nckhrdy/EchoView.ai/Device/TeensyDevDemos/Arduino/OLED_1in5_b/OLED_1in5_b.cpp

/*****************************************************************************
* | File        :   OLED_1in5_b.c
* | Author      :   Waveshare team
* | Function    :   1.5inch OLED Module (B) Drive function
* | Info        :
*----------------
* | This version:   V1.0
* | Date        :   2023-05-20
* | Info        :
* -----------------------------------------------------------------------------
#
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
******************************************************************************/
#include "OLED_1in5_b.h"
#include "stdio.h"
#include "DEV_Config.h"
/*******************************************************************************
function:
            Hardware reset
*******************************************************************************/
static void OLED_Reset(void)
{
    OLED_RST_1;
    Driver_Delay_ms(100);
    OLED_RST_0;
    Driver_Delay_ms(100);
    OLED_RST_1;
    Driver_Delay_ms(100);
}

/*******************************************************************************
function:
            Write register address and data
*******************************************************************************/
static void OLED_WriteReg(uint8_t Reg)
{
#if USE_SPI
    OLED_DC_0;
    DEV_SPI_WriteByte(Reg);
#elif USE_IIC
    I2C_Write_Byte(Reg, IIC_CMD);
#endif
}

static void OLED_WriteData(uint8_t Data)
{
#if USE_SPI
    OLED_DC_1;
    DEV_SPI_WriteByte(Data);
#elif USE_IIC
    I2C_Write_Byte(Data, IIC_RAM);
#endif
}

/*******************************************************************************
function:
            Common register initialization
*******************************************************************************/
static void OLED_InitReg(void)
{
    OLED_WriteReg(0xae); /*turn off OLED display*/
    OLED_WriteReg(0x00); /*set lower column address*/
    OLED_WriteReg(0x10); /*set higher column address*/

    OLED_WriteReg(0xB0); /*set page address*/

    OLED_WriteReg(0xdc); /*set display start line*/
    OLED_WriteReg(0x20);

    OLED_WriteReg(0x81); /*contract control*/
    OLED_WriteReg(0x6f); /*128*/

    OLED_WriteReg(0x21); /* Set Memory addressing mode (0x20/0x21) */

    OLED_WriteReg(0xa1); /*set segment remap*/

    OLED_WriteReg(0xc0); /*Com scan direction*/

    OLED_WriteReg(0xa4); /*Disable Entire Display On (0xA4/0xA5)*/

    OLED_WriteReg(0xa6); /*normal / reverse*/

    OLED_WriteReg(0xa8); /*multiplex ratio*/
    OLED_WriteReg(0x7f); /*duty = 1/64*/

    OLED_WriteReg(0xd3); /*set display offset*/
    OLED_WriteReg(0x60);

    OLED_WriteReg(0xd5); /*set osc division*/
    OLED_WriteReg(0x80);

    OLED_WriteReg(0xd9); /*set pre-charge period*/
    OLED_WriteReg(0x1d);

    OLED_WriteReg(0xdb); /*set vcomh*/
    OLED_WriteReg(0x35);

    OLED_WriteReg(0xad); /*set charge pump enable*/
    OLED_WriteReg(0x80); /*Set DC-DC enable (a=0:disable; a=1:enable) */
}

/********************************************************************************
function:
            initialization
********************************************************************************/
void OLED_1in5_B_Init()
{
    System_Init();
    // Hardware reset
    OLED_Reset();
    // Set the initialization register

    OLED_InitReg();
    Driver_Delay_ms(200);

    // Turn on the OLED display
    OLED_WriteReg(0xaf);
}

/********************************************************************************
function:
            Clear screen
********************************************************************************/
void OLED_1in5_B_Clear()
{
    UWORD Width, Height, column;
    Width = (OLED_1in5_B_WIDTH % 8 == 0) ? (OLED_1in5_B_WIDTH / 8) : (OLED_1in5_B_WIDTH / 8 + 1);
    Height = OLED_1in5_B_HEIGHT;

    OLED_WriteReg(0xb0); // Set the row  start address
    for (UWORD j = 0; j < Height; j++)
    {
        column = j;
        OLED_WriteReg(0x00 + (column & 0x0f)); // Set column low start address
        OLED_WriteReg(0x10 + (column >> 4));   // Set column higt start address
        for (UWORD i = 0; i < Width; i++)
        {
            OLED_WriteData(0x00);
        }
    }
}
void OLED_1in5_B_Clear_Black(void)
{
    UWORD Width, Height, column;
    Width = (OLED_1in5_B_WIDTH % 8 == 0) ? (OLED_1in5_B_WIDTH / 8) : (OLED_1in5_B_WIDTH / 8 + 1);
    Height = OLED_1in5_B_HEIGHT;

    OLED_WriteReg(0xb0); // Set the row  start address
    for (UWORD j = 0; j < Height; j++)
    {
        column = j;
        OLED_WriteReg(0x00 + (column & 0x0f)); // Set column low start address
        OLED_WriteReg(0x10 + (column >> 4));   // Set column higt start address
        for (UWORD i = 0; i < Width; i++)
        {
            OLED_WriteData(0xff);
        }
    }
}

/********************************************************************************
function:
            reverse a byte data
********************************************************************************/
static UBYTE reverse(UBYTE temp)
{
    temp = ((temp & 0x55) << 1) | ((temp & 0xaa) >> 1);
    temp = ((temp & 0x33) << 2) | ((temp & 0xcc) >> 2);
    temp = ((temp & 0x0f) << 4) | ((temp & 0xf0) >> 4);
    return temp;
}

/********************************************************************************
function:
    Update all memory to OLED
********************************************************************************/
void OLED_1in5_B_Display(const UBYTE *Image)
{
    UWORD Width, Height, column, temp;
    Width = (OLED_1in5_B_WIDTH % 8 == 0) ? (OLED_1in5_B_WIDTH / 8) : (OLED_1in5_B_WIDTH / 8 + 1);
    Height = OLED_1in5_B_HEIGHT;
    OLED_WriteReg(0xb0); // Set the row  start address
    for (UWORD j = 0; j < Height; j++)
    {
        // column = 63 - j;
        column = j;
        OLED_WriteReg(0x00 + (column & 0x0f)); // Set column low start address
        OLED_WriteReg(0x10 + (column >> 4));   // Set column higt start address
        for (UWORD i = 0; i < Width; i++)
        {
            temp = pgm_read_byte(&Image[i + j * Width]);
            temp = reverse(temp); // reverse the buffer
            OLED_WriteData(temp);
        }
    }
}

/********************************************************************************
function:   Update part memory to OLED
********************************************************************************/
void OLED_1in5_B_Display_Part(const UBYTE *Image, UBYTE Xstart, UBYTE Ystart, UBYTE Xend, UBYTE Yend)
{
    UWORD Width, Height, column, temp;

    Width = (OLED_1in5_B_WIDTH % 8 == 0) ? (OLED_1in5_B_WIDTH / 8) : (OLED_1in5_B_WIDTH / 8 + 1);
    Height = OLED_1in5_B_HEIGHT;

    OLED_WriteReg(0xb0); // Set the row  start address
    for (UWORD j = 0; j < Height; j++)
    {
        // column = OLED_1in5_B_HEIGHT - j;
        column = j;
        OLED_WriteReg(0x00 + (column & 0x0f)); // Set column low start address
        OLED_WriteReg(0x10 + (column >> 4));   // Set column higt start address
        for (UWORD i = 0; i < Width; i++)
        {
            if (column >= DrawBuffer_height || column > Yend || (i * 8) >= Xend || (i * 8) < Xstart || column < Ystart)
            {
                OLED_WriteData(0x00);
            }
            else
            {
                temp = (Image[i + j * (Width)]);
                temp = reverse(temp); // reverse the buffer
                OLED_WriteData(temp);
            }
        }
    }
}
/********************************************************************************
function:   OLED display test animation
********************************************************************************/
void OLED_1in5_B_Display_Test(void)
{
    UWORD Width, Height, column, temp, line;

    Width = (OLED_1in5_B_WIDTH % 8 == 0) ? (OLED_1in5_B_WIDTH / 8) : (OLED_1in5_B_WIDTH / 8 + 1);
    Height = OLED_1in5_B_HEIGHT;

    for (UWORD m = 0; m < Height; m++)
    {
        OLED_WriteReg(0xb0); // Set the row  start address
        for (UWORD j = 0; j < Height; j++)
        {
            column=j;
            OLED_WriteReg(0x00 + (column & 0x0f)); // Set column low start address
            OLED_WriteReg(0x10 + (column >> 4));   // Set column higt start address
            for (UWORD i = 0; i < Width; i++)
            {
                if (j == m)
                {
                    OLED_WriteData(0xff);
                }
                else
                {
                    OLED_WriteData(0x00);
                }
            }
        }
        Driver_Delay_ms(20);
    }

    for (UWORD m = 0; m < Width; m++)
    {
        OLED_WriteReg(0xb0); // Set the row  start address
        for (UWORD j = 0; j < Height; j++)
        {
            column=j;
            OLED_WriteReg(0x00 + (column & 0x0f)); // Set column low start address
            OLED_WriteReg(0x10 + (column >> 4));   // Set column higt start address
            for (UWORD i = 0; i < Width; i++)
            {
                if (i == m)
                {
                    OLED_WriteData(0xff);
                }
                else
                {
                    OLED_WriteData(0x00);
                }
            }
        }
        Driver_Delay_ms(50);
    }
}
