nckhrdy/EchoView.ai/Device/TeensyDevDemos/Arduino/OLED_0in95_rgb/ImageData.c

/*****************************************************************************
* | File      	:   ImageData.c
* | Author      :   Waveshare team
* | Function    :	
*----------------
* |	This version:   V1.0
* | Date        :   2020-08-19
* | Info        :
*
#
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
******************************************************************************/

#include "ImageData.h"
#include <avr/pgmspace.h>

const unsigned char gImage_0in95_rgb[12296] PROGMEM = { /*0X10,0X10,0X00,0X60,0X00,0X40,0X01,0X1B,*/
0X03,0XC8,0X03,0XC8,0X03,0XC9,0X03,0X47,0X0C,0X26,0X2D,0X25,0X3D,0X68,0X05,0X3B,
0X05,0X3F,0X0C,0XF7,0X15,0X32,0X0D,0X37,0X15,0X34,0X1D,0X2C,0X05,0X39,0X05,0X3F,
0X04,0XFC,0X05,0X3C,0X05,0X3C,0X05,0X3C,0X05,0X7D,0X25,0XFD,0X6E,0X3D,0X6E,0X3D,
0X76,0X7E,0X8E,0XBE,0X8E,0XBE,0X96,0XBE,0XCF,0X7F,0XFF,0XFF,0XA6,0X78,0X3C,0X6F,
0X03,0X0C,0X74,0XB1,0XFF,0X35,0XC4,0XEE,0X0A,0XC9,0X3B,0XCE,0X63,0X89,0X84,0X67,
0X12,0XC9,0X02,0X0A,0X02,0X8A,0X02,0X07,0X02,0X09,0X02,0XCB,0X01,0XC7,0X01,0X86,
0X02,0X09,0X01,0X45,0X01,0X85,0X02,0X08,0X01,0XC7,0X02,0X08,0X01,0XC7,0X01,0XC7,
0X01,0XC8,0X01,0X89,0X11,0X87,0X22,0XC6,0X1B,0X07,0X42,0X88,0X4A,0X86,0X3A,0X46,
0X39,0XC4,0X1A,0X89,0X02,0X4A,0X01,0XC7,0X02,0X09,0X02,0X4A,0X02,0X09,0X19,0XC7,
0X4A,0X48,0X02,0X49,0X02,0X09,0X11,0XC7,0X01,0XC8,0X02,0X09,0X02,0X8B,0X02,0X09,
0X02,0X08,0X01,0XC9,0X02,0X09,0X01,0XC8,0X01,0X86,0X01,0X45,0X01,0X46,0X09,0XC7,
0X72,0X89,0X6A,0X48,0X49,0X86,0X21,0X45,0X09,0XC7,0X09,0XC7,0X09,0X46,0X01,0X87,
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
0XFB,0X54,0XEC,0X33,0XFC,0XB5,0XFD,0X37,0XC4,0X73,0XAC,0XB2,0X73,0X4D,0X1A,0X89,
0X02,0XC9,0X03,0X4B,0X03,0X8C,0X03,0X8C,0X03,0X4B,0X21,0XC8,0X29,0X47,0X18,0XC4,
0X20,0XC5,0X29,0X87,0X19,0X47,0X21,0X49,0X21,0XCC,0X2A,0X90,0X3B,0X54,0X43,0XD6,
};
