nckhrdy/EchoView.ai/Device/TeensyDevDemos/Arduino/OLED_0in96_rgb/ImageData.c

/*****************************************************************************
* | File      	:   ImageData.c
* | Author      :   Waveshare team
* | Function    :	
*----------------
* |	This version:   V1.0
* | Date        :   2020-08-19
* | Info        :
*
#
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
******************************************************************************/

#include "ImageData.h"
#include <avr/pgmspace.h>

const unsigned char gImage_0in96_rgb[16384] PROGMEM = {
0X08,0X86,0X08,0X86,0X08,0X86,0X08,0X86,0X08,0X86,0X08,0X86,0X08,0X86,0X08,0X86,
0X08,0X86,0X08,0X86,0X10,0X86,0X10,0X86,0X10,0X86,0X10,0X86,0X21,0X07,0X08,0X86,
0X08,0X86,0X10,0X86,0X10,0X86,0X10,0X86,0X08,0X86,0X08,0X86,0X08,0X86,0X08,0X86,
0X08,0X86,0X08,0X87,0X08,0X86,0X08,0X86,0X18,0XC8,0X08,0X86,0X08,0X86,0X08,0X87,
0X08,0X87,0X08,0X87,0X08,0X87,0X08,0X86,0X10,0X86,0X29,0X49,0X10,0X86,0X10,0X86,
0X10,0X87,0X10,0XC6,0X10,0XC6,0X10,0XC6,0X10,0XC6,0X10,0XC6,0X10,0XC6,0X10,0XC6,
0X18,0XC6,0X18,0XC6,0X18,0XC6,0X18,0XC6,0X18,0XC6,0X18,0XC7,0X18,0XC7,0X18,0XC7,
0X18,0XC7,0X18,0XC7,0X18,0XC6,0X7A,0X45,0XE4,0XA8,0X31,0X47,0X18,0XC7,0X19,0X07,
0X08,0X86,0X08,0X86,0X08,0X86,0X08,0X86,0X08,0X86,0X08,0X86,0X08,0X86,0X08,0X86,
0X08,0X86,0X08,0X86,0X08,0X86,0X10,0X86,0X10,0X86,0X10,0X86,0X08,0X86,0X08,0X86,
0X08,0X86,0X10,0X86,0X10,0X85,0X52,0X0A,0X08,0X86,0X08,0X86,0X08,0X87,0X08,0X87,
0X08,0X87,0X08,0X87,0X08,0X87,0X08,0X87,0X08,0X87,0X08,0X87,0X08,0X87,0X08,0X87,
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
0XC7,0X39,0XFF,0X7A,0XFF,0X7A,0XFF,0X79,0XFF,0X79,0XFF,0X79,0XFF,0X79,0XFF,0X78,
0XFE,0XB1,0XFD,0XA7,0XFC,0X20,0XF3,0XC0,0XFB,0XC0,0XFB,0X80,0XFB,0X80,0XFB,0X80,
0XFB,0X80,0XFB,0X80,0XFB,0X80,0XFB,0X80,0XFB,0X80,0XFB,0X80,0XFB,0X80,0XFB,0X80,
};
