nckhrdy/EchoView.ai/Device/TeensyDevDemos/Arduino/OLED_1in27_rgb/ImageData.c

/*****************************************************************************
* | File      	:   ImageData.c
* | Author      :   Waveshare team
* | Function    :	
*----------------
* |	This version:   V1.0
* | Date        :   2020-08-19
* | Info        :
*
#
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
******************************************************************************/

#include "ImageData.h"
#include <avr/pgmspace.h>

const unsigned char gImage_1in5_rgb[7208] PROGMEM = { /*0X10,0X10,0X00,0X3C,0X00,0X3C,0X01,0X1B,*/
0X83,0X0A,0XA3,0X8B,0X33,0X4B,0X12,0X48,0X01,0X84,0X02,0X46,0X03,0X08,0X23,0X08,
0X32,0X46,0X02,0XC5,0X04,0X6B,0X05,0X2B,0X0C,0X68,0X01,0XC2,0X03,0X07,0X04,0X6B,
0X04,0X68,0X1D,0X30,0XEF,0XFF,0X75,0XF1,0X14,0X66,0X44,0X6B,0X03,0X00,0X1B,0X84,
0X23,0X45,0X0A,0X46,0XB5,0X75,0XF7,0X7D,0XEF,0XBD,0XFF,0XFF,0X9B,0X4D,0X01,0X4C,
0X22,0X4B,0XAC,0XF1,0X8C,0X71,0XAD,0X74,0XB5,0XB6,0X4A,0X49,0X7B,0XCD,0XA4,0XF1,
0X7B,0XCE,0XDE,0XFA,0XAD,0X73,0XB5,0X75,0XCE,0X78,0X84,0X2F,0X6B,0X8D,0X63,0X0B,
0XAB,0XC8,0X79,0X80,0X9C,0X71,0XFF,0XFF,0XDE,0XBA,0XF7,0X7D,0XFF,0XFF,0XFF,0XFF,
0XE7,0X3C,0XB5,0XB7,0X54,0X30,0X03,0X4A,0X93,0X4A,0X93,0X8B,0X92,0X47,0X31,0X44,
0X01,0X43,0X02,0X87,0X02,0X87,0X02,0XC6,0X3A,0XC7,0X23,0X47,0X04,0X2B,0X0C,0XF6,
0X0D,0X77,0X1C,0X25,0X02,0XC2,0X14,0X2C,0X1D,0XB5,0X4D,0XFB,0XCF,0X7F,0X4D,0X2A,
0X96,0XB3,0XDE,0XFD,0X3A,0XCA,0X12,0X48,0X3B,0X0A,0X5B,0X8D,0XBE,0X37,0XE7,0X3C,
0XC5,0XF7,0XB5,0XB6,0XBD,0XB5,0X8C,0XF3,0X94,0XB2,0XD6,0X38,0XA5,0X33,0XB5,0XB6,
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
0X49,0XC7,0X5C,0XEE,0XFF,0XFF,0XFF,0XFC,0XB6,0X75,0X63,0XCC,0X00,0X41,0X31,0X03,
0X73,0X0E,0X2C,0X2F,0X1C,0X6F,0X3B,0X8D,0X42,0X8A,0X54,0X2B,0X94,0XEE,0X9A,0XCC,
0X8D,0X66,0X8E,0X25,0X8D,0X68,0X95,0X6A,0X9C,0XAE,0XAC,0XB1,0XA4,0X6D,0XCE,0X35,
};
