nckhrdy/EchoView.ai/Device/TeensyDevDemos/Arduino/OLED_1in32/ImageData.c

/*****************************************************************************
* | File      	:   ImageData.c
* | Author      :   Waveshare team
* | Function    :	
*----------------
* |	This version:   V1.0
* | Date        :   2020-08-19
* | Info        :
*
#
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
******************************************************************************/

#include "ImageData.h"
#include <avr/pgmspace.h>


const unsigned char gImage_1in32[6150] PROGMEM = { /*0X00,0X04,0X80,0X00,0X60,0X00,*/
0X00,0X88,0X00,0X88,0X80,0X00,0X00,0X00,0X80,0X00,0X80,0X80,0X08,0X80,0X0C,0X08,
0X8C,0X08,0X8C,0XCC,0XF8,0X88,0X08,0X08,0X80,0X88,0X88,0X88,0X8C,0XCC,0XCC,0XCF,
0XC0,0X08,0X08,0XCC,0X88,0XCC,0XCC,0X80,0X08,0X88,0X80,0XCF,0XCC,0XF8,0X8F,0XFC,
0X00,0X8C,0XF8,0X08,0X08,0XCF,0XFF,0XCC,0XFF,0XFF,0XFF,0XFC,0X88,0X88,0X88,0X88,
0X08,0X80,0X88,0X88,0X00,0X00,0X00,0X00,0X08,0X00,0X00,0X88,0X88,0X80,0X00,0X00,
0X88,0X08,0X88,0XCC,0XFC,0X08,0X88,0X88,0X88,0X88,0X80,0X00,0X8C,0XCC,0XCC,0XCC,
0XC8,0X88,0X00,0X88,0X88,0X8C,0XC8,0X80,0X00,0X88,0XC8,0X8F,0XCC,0XF8,0X8F,0XCC,
0X88,0X00,0X00,0X08,0X80,0X08,0XFF,0XF8,0XFF,0XFF,0XFF,0XFF,0XC8,0X88,0X88,0X88,
0X08,0X80,0X00,0X00,0X00,0X00,0X00,0X00,0X00,0X00,0X88,0X88,0X88,0X80,0X00,0X08,
0X08,0X88,0X88,0XCC,0XFC,0X08,0X8C,0X08,0X00,0X88,0X80,0X08,0X8F,0XCC,0XCC,0XCC,
0XC0,0X88,0X00,0X08,0XC8,0X08,0XCC,0X80,0X08,0X88,0XC8,0X0C,0XFC,0XF8,0X8F,0XFF,
0X88,0X88,0X80,0X8C,0X88,0X00,0XCF,0XFC,0XCF,0XCF,0XFF,0XFF,0XFF,0XFC,0X80,0X88,
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
0X88,0XC8,0X80,0X08,0X8F,0XCC,0XCC,0XC8,0X00,0X00,0X00,0X00,0X8C,0XCC,0X8C,0X88,
0X00,0X88,0X88,0X80,0X00,0X88,0X88,0X00,0X80,0X00,0X0C,0X88,0X88,0X08,0XCC,0XC8,
0X08,0X88,0X8C,0X8C,0XC8,0X8C,0X88,0XC8,0X88,0X88,0X88,0X80,0X00,0X00,0X00,0X00,
};
