nckhrdy/EchoView.ai/Device/TeensyDevDemos/Arduino/OLED_1in5/ImageData.c

/*****************************************************************************
* | File      	:   ImageData.c
* | Author      :   Waveshare team
* | Function    :	
*----------------
* |	This version:   V1.0
* | Date        :   2020-08-19
* | Info        :
*
#
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
******************************************************************************/

#include "ImageData.h"
#include <avr/pgmspace.h>

const unsigned char gImage_1in5[8198] PROGMEM = { /*0X00,0X04,0X80,0X00,0X80,0X00,*/
0X33,0X66,0X33,0X44,0X43,0X31,0X33,0X33,0X73,0X13,0X63,0X63,0X34,0X61,0X3C,0X36,
0X4A,0X37,0X7A,0XAD,0XF7,0X65,0X16,0X36,0X63,0X67,0X77,0X77,0X7A,0XDD,0XDD,0XDF,
0XA3,0X34,0X17,0XDA,0X77,0XAA,0XAA,0X73,0X36,0X67,0X73,0XAF,0XDD,0XF6,0X7F,0XFD,
0X33,0X7A,0XF7,0X36,0X37,0XDF,0XFF,0XAA,0XFF,0XFF,0XFF,0XFA,0X44,0X44,0X47,0X44,
0X16,0X63,0X44,0X46,0X31,0X33,0X33,0X33,0X36,0X33,0X33,0X66,0X56,0X63,0X33,0X33,
0X46,0X34,0X46,0XAD,0XFA,0X36,0X66,0X56,0X66,0X66,0X63,0X13,0X7A,0XDD,0XDD,0XAA,
0XA6,0X47,0X33,0X77,0X77,0X7A,0XA7,0X73,0X13,0X77,0XD6,0X6F,0XDD,0XF6,0X7F,0XDD,
0X66,0X31,0X31,0X36,0X63,0X17,0XFF,0XF7,0XFF,0XFF,0XFF,0XFF,0XA7,0X77,0X44,0X46,
0X17,0X63,0X33,0X31,0X11,0X33,0X33,0X33,0X13,0X33,0X66,0X66,0X66,0X63,0X31,0X36,
0X36,0X66,0X66,0XAD,0XFA,0X36,0X7A,0X35,0X31,0X66,0X63,0X34,0X7F,0XDD,0XDD,0XDD,
0XA3,0X47,0X11,0X17,0XD6,0X36,0XAA,0X73,0X16,0X67,0XA6,0X3A,0XFD,0XF7,0X6F,0XFF,
0X67,0X77,0X63,0X6C,0X66,0X31,0XAF,0XFA,0XDF,0XDF,0XFF,0XFF,0XFF,0XFD,0X73,0X44,
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
0X66,0X66,0X66,0X66,0X66,0X63,0X35,0X63,0X66,0X66,0X66,0X66,0X66,0X66,0X66,0X63,
0X63,0X66,0X66,0X36,0X16,0X66,0X66,0X13,0X7D,0XDF,0XFD,0XA3,0X11,0X11,0X17,0X11,
0X33,0X33,0X33,0X11,0X11,0X36,0X73,0X66,0X6C,0X66,0X67,0XC3,0X6A,0XA6,0X77,0XCA,
};
