nckhrdy/EchoView.ai/Device/TeensyDevDemos/Arduino/OLED_1in5_b/ImageData.c

#include "ImageData.h"
#include <avr/pgmspace.h>

const unsigned char IMAGE_1in5B [2048] PROGMEM= { 
0XFF,0XFF,0XFF,0XFF,0XC3,0XFF,0X83,0XFF,0X18,0X00,0X00,0X01,0X3F,0XFF,0XFF,0XFC,
0XFF,0XFF,0XFF,0XFF,0XC7,0XFF,0X07,0XFE,0X30,0X00,0X00,0X01,0X3F,0XFF,0XFF,0XF8,
0XFF,0XFF,0XFF,0XFF,0XC7,0XFE,0X0F,0XFE,0X20,0X00,0X00,0X03,0X3F,0XFF,0XFF,0XF0,
0XFF,0XFF,0XFF,0XFF,0XC7,0XFC,0X1F,0XFC,0X60,0X00,0X00,0X03,0X3F,0XFF,0XFF,0XC0,
0XFF,0XFF,0XFF,0XFF,0XC7,0XFC,0X3F,0XFC,0X40,0X00,0X00,0X02,0X7F,0XFF,0XFF,0X81,
0XFF,0XFF,0XFF,0XFF,0X87,0XF8,0X7F,0XF8,0X40,0X00,0X00,0X02,0X7F,0XFF,0XFF,0X03,
0XFF,0XFF,0XFF,0XFF,0X8F,0XF8,0XFF,0XF8,0X00,0X00,0X00,0X06,0X7F,0XFF,0XFE,0X07,
0XFF,0XFF,0XFF,0XFF,0X8F,0XF0,0XFF,0XF0,0X00,0X00,0X00,0X06,0X7F,0XFF,0XFC,0X1F,
0XFF,0XFF,0XFF,0XFF,0X8F,0XF1,0XFF,0XF0,0X00,0X00,0X00,0X06,0X7F,0XFF,0XF0,0X3F,
0XFF,0XFF,0XFF,0XFF,0X8F,0XF1,0XFF,0XE0,0X00,0X00,0X00,0X0C,0X7F,0XFF,0XC0,0X7F,
0XFF,0XFF,0XFF,0XFF,0X8F,0XE1,0XFF,0XE0,0X00,0X00,0X00,0X0C,0XFF,0XFF,0X01,0XFF,
0XFF,0XFF,0XFF,0XFF,0X8F,0XE3,0XF9,0XE0,0X70,0X00,0X00,0X0C,0XFF,0XFC,0X03,0XFF,
0XFF,0XFF,0XFF,0XFF,0X87,0XE3,0XF8,0X00,0X7E,0X00,0X00,0X1C,0XFF,0XE0,0X1F,0XFF,
0XFF,0XFF,0XFF,0XFF,0X87,0XE3,0XF8,0X00,0XFF,0XC0,0X00,0X19,0XFF,0X80,0X7F,0XFF,
0XFF,0XFF,0XFF,0XFF,0XC7,0XE3,0XF1,0X01,0XFF,0XF8,0X00,0X39,0XFE,0X01,0XFF,0XFF,
0XFF,0XFF,0XFF,0XFF,0XC7,0XE3,0XF1,0XF1,0XFF,0XFE,0X00,0X39,0XF8,0X0F,0XFF,0XFF,
0XFF,0XFF,0XFF,0XFF,0XC7,0XE7,0XE3,0XF3,0XFF,0XFF,0X80,0X39,0XE0,0X3F,0XFF,0XFF,
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
0XFF,0XFF,0XFF,0XFF,0XFF,0X9E,0X61,0XFF,0XC0,0XFF,0XFF,0XFF,0XFF,0XF0,0X1F,0XFF,
0XFF,0XFF,0XFF,0XFF,0XFF,0XCF,0X31,0XFF,0XE0,0X3F,0XFF,0XFF,0XFF,0X80,0X7F,0XFF,
0XFF,0XFF,0XFF,0XFF,0XFF,0XE3,0X91,0XFF,0XE0,0X07,0XFF,0XFF,0XFC,0X01,0XFF,0XFF,
};
