nckhrdy/EchoView.ai/Device/TeensyDevDemos/ESP32/OLED_1in54/ImageData.c

/*****************************************************************************
* | File      	:   ImageData.c
* | Author      :   Waveshare team
* | Function    :	
*----------------
* |	This version:   V1.0
* | Date        :   2020-08-19
* | Info        :
*
#
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
******************************************************************************/

#include "ImageData.h"
#include <pgmspace.h>

const unsigned char gImage_1in3[1030] PROGMEM = { /*0X00,0X01,0X40,0X00,0X80,0X00,*/
0X00,0X00,0X00,0X00,0X00,0X00,0X00,0X00,0X00,0X00,0X00,0X00,0X00,0X00,0X00,0X00,
0X00,0X00,0X00,0X00,0X00,0X00,0X00,0X00,0X00,0X00,0X00,0X00,0X00,0X00,0X00,0X00,
0X00,0X00,0X00,0X00,0X78,0X00,0X00,0X00,0X00,0X00,0X00,0X00,0XFE,0X00,0X00,0X00,
0X00,0X00,0X00,0X01,0XC7,0X00,0X00,0X00,0X00,0X00,0X00,0X03,0X83,0X80,0X70,0X00,
0X00,0X00,0X1F,0X07,0X01,0X83,0XFE,0X00,0X00,0X00,0X3F,0XC6,0X01,0XCF,0X8F,0X00,
0X00,0X00,0X30,0XE6,0X00,0XFC,0X03,0X00,0X00,0X00,0X70,0X7E,0X00,0XF0,0X03,0X00,
0X00,0X00,0X60,0X3C,0X00,0X60,0X03,0X00,0X00,0X00,0X60,0X1C,0X00,0X00,0X03,0X00,
0X00,0X00,0X60,0X0C,0X00,0X00,0X07,0X00,0X00,0X00,0X70,0X0C,0X00,0X00,0X06,0X00,
0X00,0X00,0X30,0X00,0X00,0X00,0X0E,0X00,0X00,0X00,0X30,0X00,0X42,0X00,0X0C,0X00,
0X00,0X00,0X38,0X00,0X42,0X00,0X1C,0X00,0X00,0X00,0X18,0X00,0X66,0X00,0X38,0X00,
0X00,0X00,0X1C,0X00,0X6E,0X00,0X70,0X00,0X00,0X00,0X0F,0X00,0X3C,0X01,0XE0,0X00,
0X00,0X00,0X07,0XF8,0X10,0X7F,0XC0,0X00,0X00,0X00,0X07,0XE0,0X00,0X1F,0X00,0X00,
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
0XFF,0XFF,0XFF,0XFF,0XFF,0X07,0XFF,0XFF,0XFF,0XFF,0XFF,0XFF,0XFF,0X8F,0XFF,0XFF,
0XFF,0XFF,0XFF,0XFF,0XFF,0XFF,0XFF,0XFF,0XFF,0XFF,0XFF,0XFF,0XFF,0XFF,0XFF,0XFF,
0XFF,0XFF,0XFF,0XFF,0XFF,0XFF,0XFF,0XFF,0XFF,0XFF,0XFF,0XFF,0XFF,0XFF,0XFF,0XFF,
};
