nckhrdy/EchoView.ai/Device/TeensyDevDemos/Arduino/OLED_1in3_c/ImageData.c

/*****************************************************************************
* | File      	:   ImageData.c
* | Author      :   Waveshare team
* | Function    :	
*----------------
* |	This version:   V1.0
* | Date        :   2020-08-19
* | Info        :
*
#
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
******************************************************************************/

#include "ImageData.h"
#include <avr/pgmspace.h>

const unsigned char gImage_1in3_c[2560] PROGMEM = { /*0X00,0X01,0X80,0X00,0X40,0X00,*/
0X00,0X00,0X00,0X00,0X00,0X10,0X00,0X00,0X00,0X00,0X00,0X00,0X00,0X00,0X00,0X00,
0X00,0X00,0X00,0X00,0X00,0X10,0X00,0X00,0X00,0X00,0X00,0X00,0X00,0X00,0X00,0X00,
0X00,0X00,0X00,0X00,0X00,0X10,0X00,0X00,0X00,0X00,0X00,0X00,0X00,0X00,0X00,0X00,
0X00,0X00,0X00,0X00,0X00,0X10,0X00,0X00,0X00,0X00,0X00,0X00,0X00,0X00,0X00,0X00,
0X00,0X00,0X00,0X00,0X00,0X10,0X00,0X00,0X00,0X00,0X00,0X00,0X00,0X00,0X00,0X00,
0X00,0X0C,0X6F,0X03,0X00,0X10,0X00,0X00,0X00,0X00,0X00,0X00,0X00,0X00,0X00,0X00,
0X00,0X0C,0X63,0X03,0X00,0X10,0X00,0X00,0X00,0X00,0X00,0X00,0X00,0X00,0X00,0X00,
0X00,0X0C,0X63,0X06,0X00,0X10,0X00,0X00,0X00,0X00,0X00,0X00,0X00,0X00,0X00,0X00,
0X00,0X0C,0X63,0X06,0X00,0X10,0X00,0X00,0X00,0X00,0X00,0X00,0X00,0X00,0X00,0X00,
0X00,0X0C,0X63,0X06,0X00,0X10,0X00,0X00,0X00,0X00,0X00,0X00,0X00,0X00,0X00,0X00,
0X00,0X0C,0XE3,0X0C,0X00,0X10,0X00,0X07,0X00,0X1F,0X83,0X8F,0XFE,0X0E,0X00,0X00,
0X00,0X07,0XEF,0X8C,0X00,0X10,0X00,0X07,0X00,0X7F,0XC3,0X8F,0XFE,0X0E,0X00,0X00,
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
0X00,0X00,0X00,0X00,0X00,0X00,0X00,0X00,0X00,0X08,0X04,0X00,0X00,0X00,0X00,0X00,
0X00,0X00,0X00,0X00,0X00,0X00,0X00,0X00,0X00,0X00,0X04,0X00,0X00,0X00,0X00,0X00,
0X00,0X00,0X00,0X00,0X00,0X00,0X00,0X00,0X00,0X00,0X04,0X00,0X00,0X00,0X00,0X00,
};
