nckhrdy/EchoView.ai/Device/TeensyDevDemos/Arduino/OLED_0in91/ImageData.c

/*****************************************************************************
* | File      	:   ImageData.c
* | Author      :   Waveshare team
* | Function    :	
*----------------
* |	This version:   V1.0
* | Date        :   2020-08-19
* | Info        :
*
#
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
******************************************************************************/

#include "ImageData.h"
#include <avr/pgmspace.h>

const unsigned char gImage_0in91[518] PROGMEM = { /*0X00,0X01,0X20,0X00,0X80,0X00,*/
0X00,0X00,0X00,0X00,0X00,0X00,0X00,0X00,0X00,0X00,0X00,0X00,0X00,0X00,0X00,0X00,
0X00,0X00,0X00,0X00,0X00,0X00,0X00,0X00,0X00,0X00,0X00,0X00,0X00,0X00,0X00,0X00,
0X00,0X00,0X00,0X00,0X00,0X00,0X00,0X00,0X00,0X00,0X00,0X00,0X00,0X00,0X00,0X00,
0X00,0X00,0X00,0X00,0X00,0X00,0X00,0X00,0X00,0X00,0X00,0X00,0X00,0X00,0X00,0X00,
0X00,0X01,0XC1,0X80,0X00,0X00,0XE1,0XC0,0X01,0XFF,0XF8,0XE0,0X01,0XFF,0XFE,0X78,
0X00,0X40,0X0E,0X38,0X00,0XE0,0X00,0X00,0X00,0X7C,0X37,0XE0,0X00,0X3F,0XB3,0XE0,
0X00,0X01,0XB2,0X00,0X00,0X01,0XB3,0XF8,0X00,0X3F,0XB3,0XF8,0X01,0XBF,0XB2,0X00,
0X01,0X98,0X33,0XE0,0X01,0XCC,0X07,0XE0,0X00,0XE0,0X3C,0X00,0X00,0X73,0XFF,0X80,
0X00,0X3F,0X87,0XF8,0X00,0X3E,0X03,0X78,0X00,0X7F,0XFF,0X00,0X00,0XE1,0XFF,0X00,
0X01,0XC0,0X03,0X00,0X01,0XC0,0X03,0X00,0X00,0X00,0X00,0X00,0X00,0X00,0X00,0X00,
0X00,0X00,0X00,0X00,0X00,0X00,0X00,0X00,0X00,0X00,0X0F,0X80,0X00,0X00,0X0F,0XB0,
0X01,0X9B,0X21,0XB0,0X01,0X93,0X2D,0XB0,0X01,0X93,0X2D,0X30,0X01,0X93,0X2D,0X30,
0X01,0X93,0X2D,0X30,0X01,0X93,0X2D,0X30,0X01,0X93,0X01,0X30,0X01,0X93,0X7F,0XF0,
0X01,0X93,0X7F,0XF0,0X01,0X93,0X01,0X30,0X01,0X93,0X25,0X30,0X01,0X93,0X25,0X30,
0X01,0X93,0X25,0X30,0X01,0X9B,0X25,0X30,0X03,0XFF,0X25,0X30,0X03,0XFF,0X21,0XB0,
0X00,0X00,0X0F,0XB0,0X00,0X00,0X0F,0X80,0X00,0X00,0X00,0X00,0X00,0X00,0X00,0X00,
0X00,0X00,0X00,0X00,0X00,0X00,0X00,0X00,0X00,0X00,0X00,0X00,0X00,0X00,0X00,0X00,
0X00,0X1F,0XFF,0XC0,0X00,0X1F,0XFF,0XC0,0X00,0X02,0X10,0XC0,0X00,0X02,0X10,0XC0,
0X00,0X02,0X10,0X80,0X00,0X02,0X10,0X80,0X00,0X02,0X10,0X80,0X00,0XFF,0XFF,0XF8,
0X00,0XFF,0XFF,0XF8,0X00,0XC7,0X39,0XC8,0X00,0X82,0X10,0X80,0X01,0X82,0X10,0X80,
0X01,0X82,0X10,0X80,0X01,0X82,0X10,0XC0,0X01,0X87,0X39,0XC0,0X01,0X8F,0XFF,0XC0,
0X00,0X8F,0XFF,0XC0,0X00,0XC0,0X00,0X00,0X00,0XF0,0X00,0X00,0X00,0XE0,0X00,0X00,
0X00,0X20,0X00,0X00,0X00,0X00,0X00,0X00,0X00,0X00,0X00,0X00,0X00,0X00,0X60,0X00,
0X00,0X00,0X60,0X00,0X00,0X00,0X60,0X00,0X00,0X00,0X60,0X30,0X00,0X00,0X60,0X30,
0X00,0X00,0X60,0X30,0X00,0X00,0X60,0X30,0X01,0X80,0X60,0X30,0X01,0X80,0X60,0X30,
0X01,0XC0,0X60,0X30,0X01,0XFF,0XFE,0X30,0X00,0XFF,0XFE,0X30,0X00,0X00,0X77,0X30,
0X00,0X00,0X63,0XB0,0X00,0X00,0X61,0XF0,0X00,0X00,0X61,0XF0,0X00,0X00,0X60,0XF0,
0X00,0X00,0X60,0X70,0X00,0X00,0X60,0X70,0X00,0X00,0X60,0X00,0X00,0X00,0X60,0X00,
0X00,0X00,0X60,0X00,0X00,0X00,0X00,0X00,0X00,0X00,0X00,0X00,0X00,0X00,0X00,0X00,
0X00,0X00,0X00,0X00,0X00,0X00,0X00,0X00,0X00,0X00,0X00,0X00,0X00,0X00,0X00,0X00,
0X00,0X00,0X00,0X00,0X00,0X00,0X00,0X00,0X00,0X00,0X00,0X00,0X00,0X00,0X00,0X00,
0X00,0X00,0X00,0X00,0X00,0X00,0X00,0X00,0X00,0X00,0X00,0X00,0X00,0X00,0X00,0X00,
};
